wgbowley/PreCharger/1-deliverable-system/pcb.png

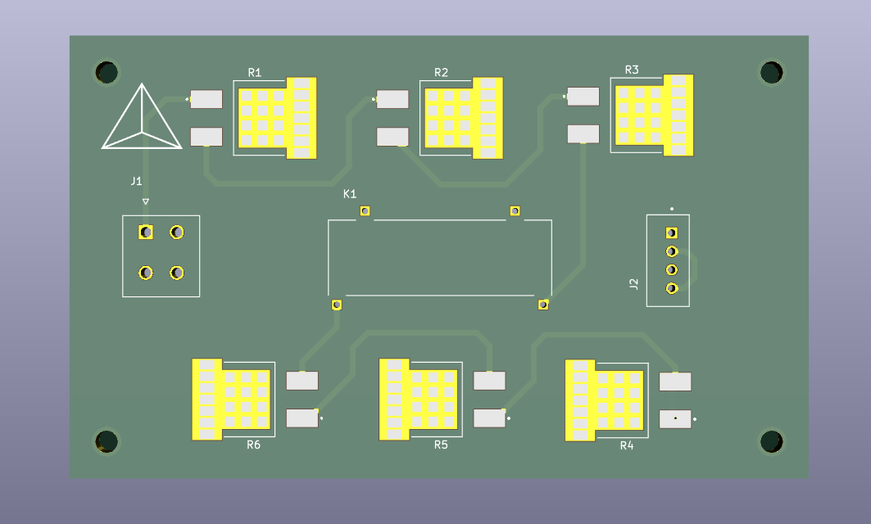
1-deliverable-system/pcb.png
