wgbowley/PreCharger/2-exploration/images/active_vs_passive_1A_50W_5S.png

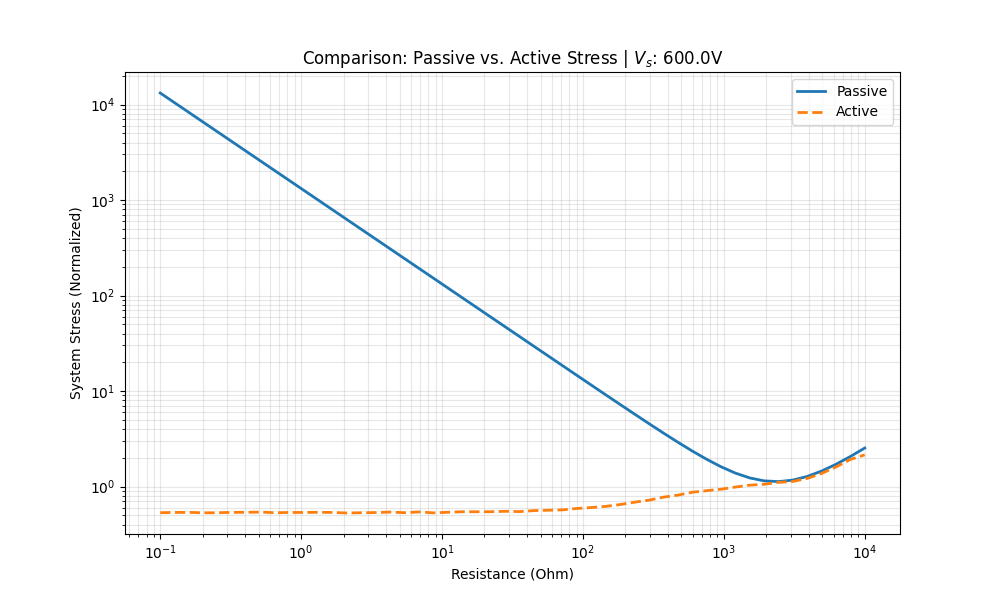
2-exploration/images/active_vs_passive_1A_50W_5S.png
