wgbowley/PreCharger/2-exploration/images/comparator_hyst.png

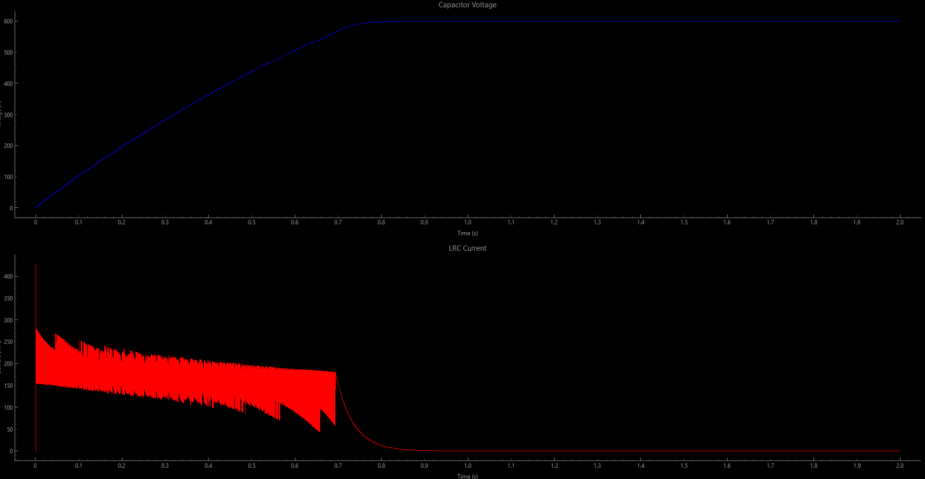
2-exploration/images/comparator_hyst.png
