wgbowley/PreCharger/2-exploration/simulation/spice/active_charger.asc

C1: cap; 240µ
D1: diode
D2: diode
L1: ind; 3m; Rser=150m
R1: res; 10k
R2: res; 100k
R3: res; 5
R4: res; 15k
R5: res; 6k
R6: res; 1G
U1: E3M0160120K
U2: UCC27517
U3: TLV7011
V1: voltage; 600
V2: voltage; 15
V3: voltage; 5
Named nets: PMW, VSSS, sense, 0
Pre-charger driver (floating gnd | VSSS)
Constant Current | Bang Bang Controller
.tran 0 1s 0 100n uic
.options method=gear
.options chgtol=1e-12
